GClown25/BIT4/hardware/v1.0/pcb_bot.PNG

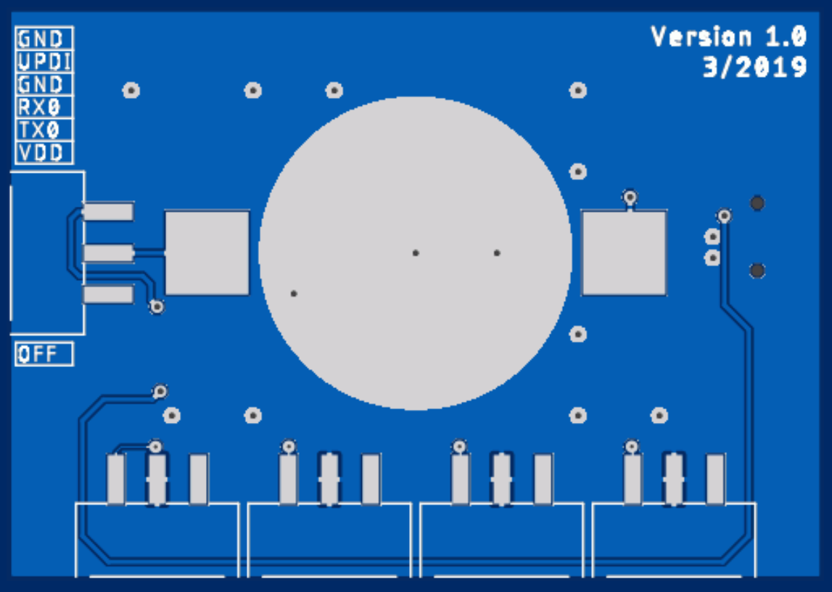
hardware/v1.0/pcb_bot.PNG
