GClown25/BIT4/hardware/v1.0/pcb_top.PNG

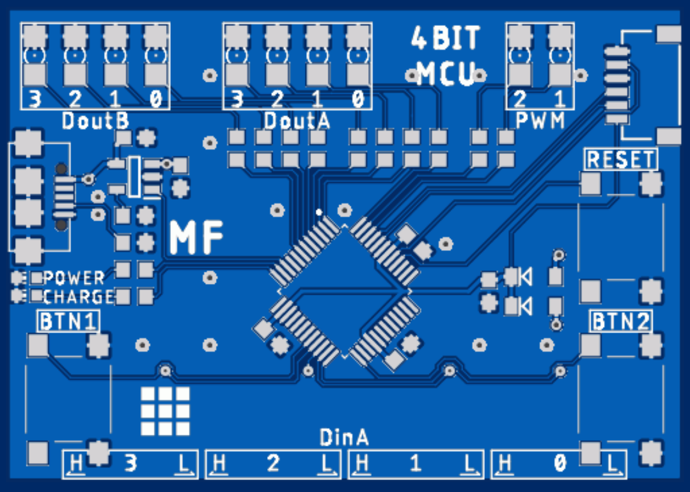
hardware/v1.0/pcb_top.PNG
