GClown25/BIT4/hardware/v1.1b/place_bot.png

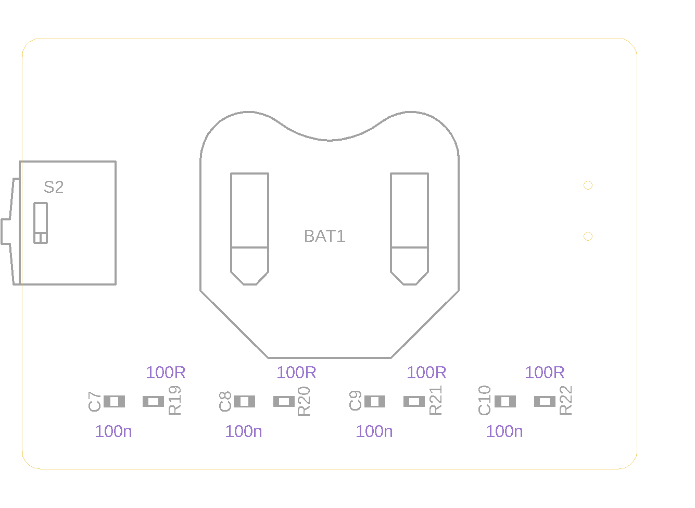
hardware/v1.1b/place_bot.png
