GClown25/BIT4/hardware/v1.1b/place_top.png

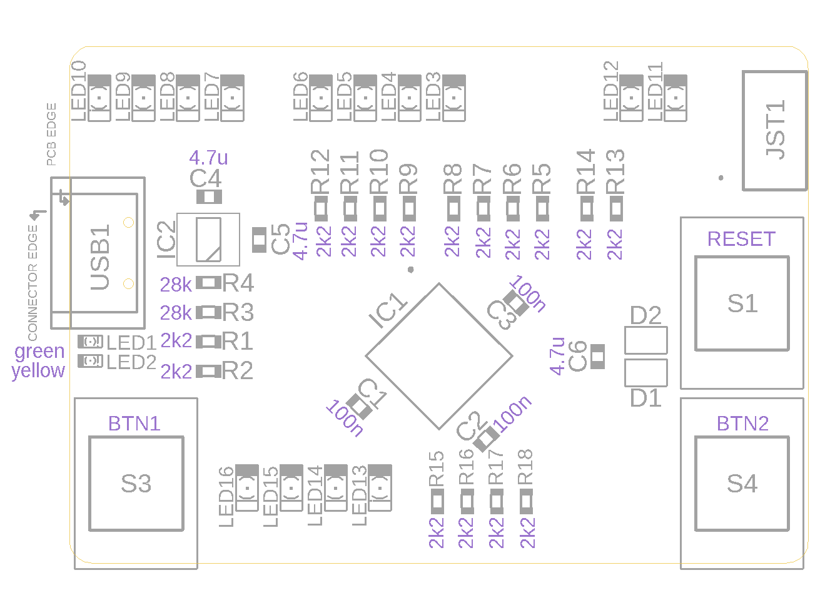
hardware/v1.1b/place_top.png
