GClown25/BIT4/hardware/v1.1b/schematic_3.png

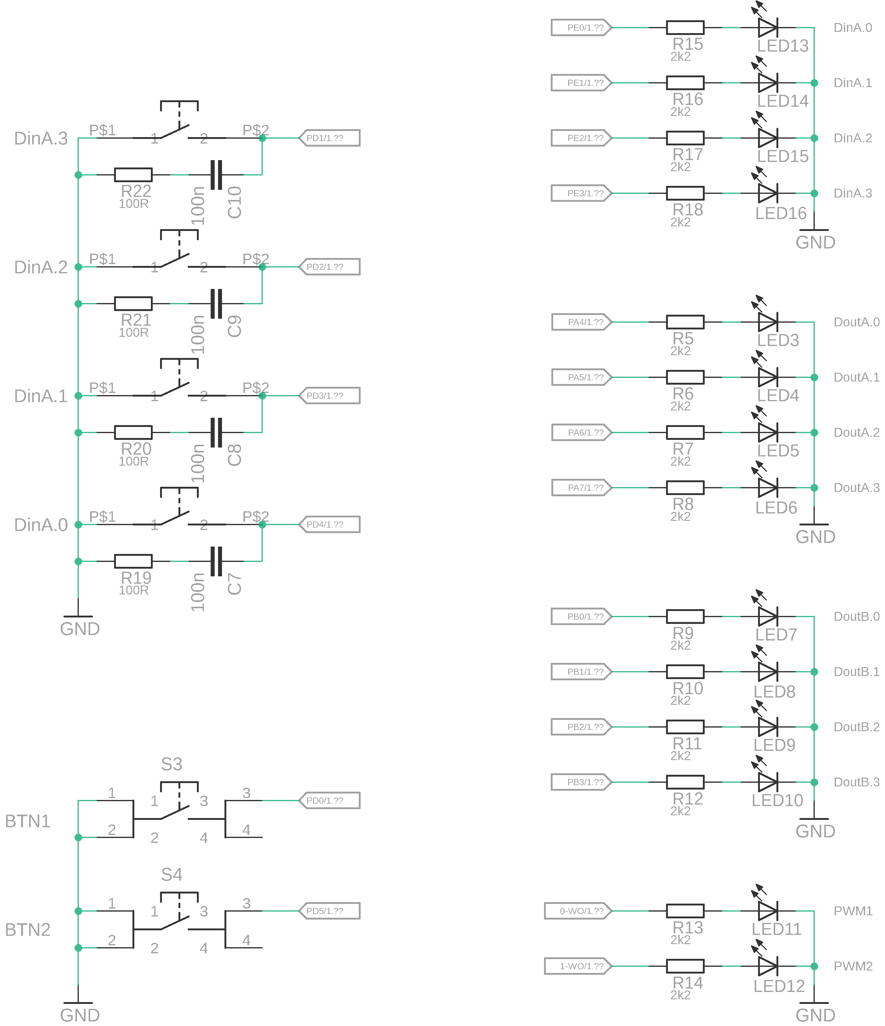
hardware/v1.1b/schematic_3.png
