GClown25/BIT4/img/BIT4.jpg

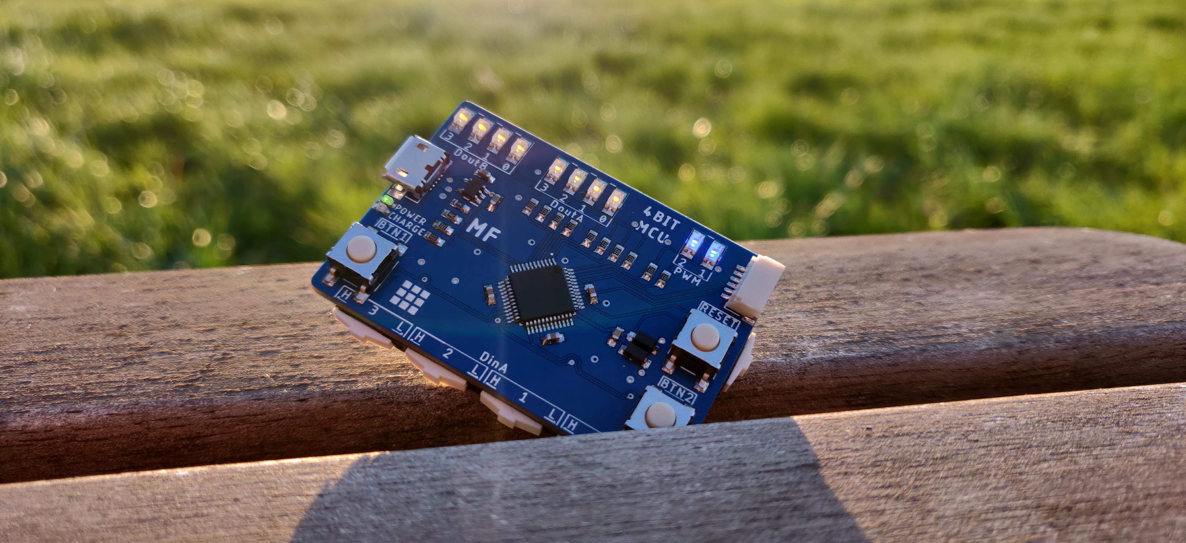
img/BIT4.jpg
